gentlegiantJGC/A-Series-of-Unfortunate-Events-Spyglass/Photos/full_1.jpg

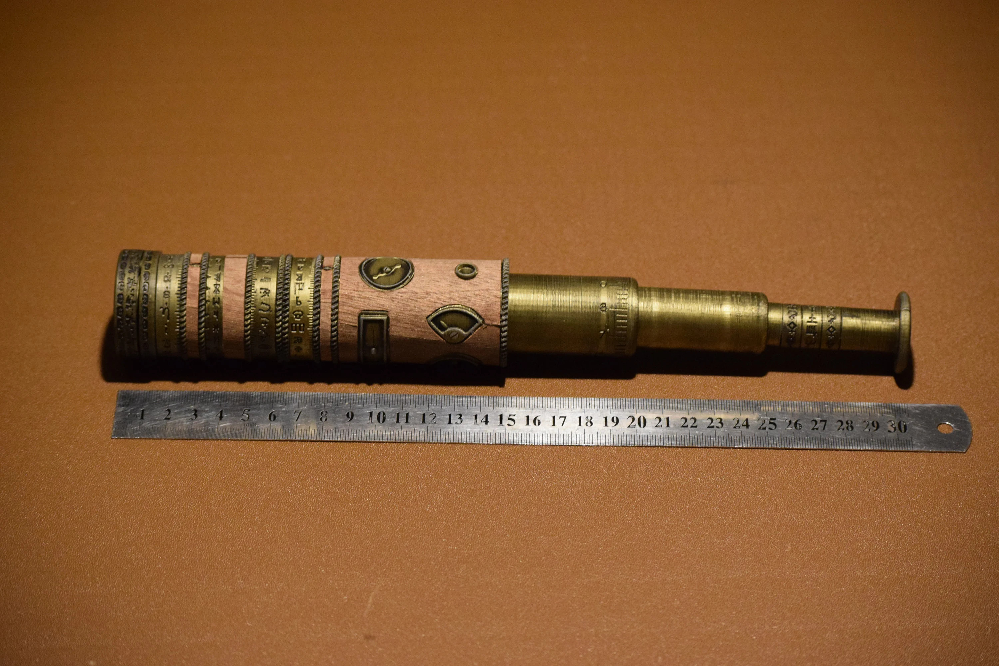
Photos/full_1.jpg
