gentlegiantJGC/A-Series-of-Unfortunate-Events-Spyglass/Photos/full_2.jpg

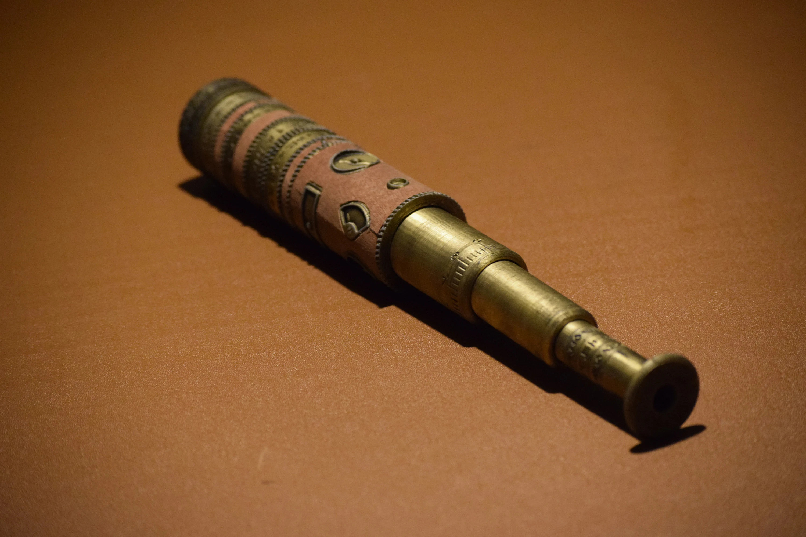
Photos/full_2.jpg
