gentlegiantJGC/A-Series-of-Unfortunate-Events-Spyglass/Photos/head_3.jpg

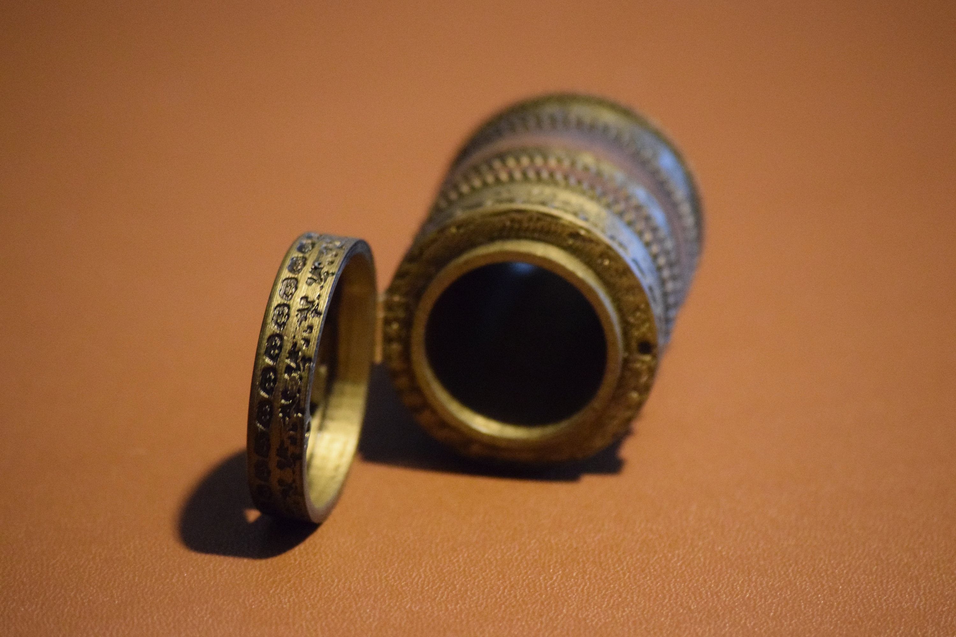
Photos/head_3.jpg
