gentlegiantJGC/A-Series-of-Unfortunate-Events-Spyglass/Photos/head_4.jpg

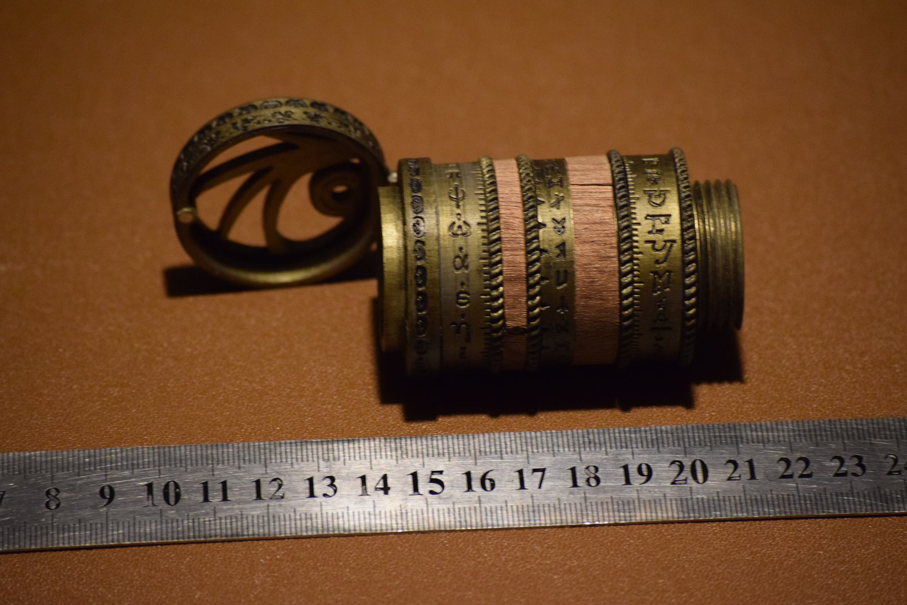
Photos/head_4.jpg
