gentlegiantJGC/A-Series-of-Unfortunate-Events-Spyglass/Photos/head_5.jpg

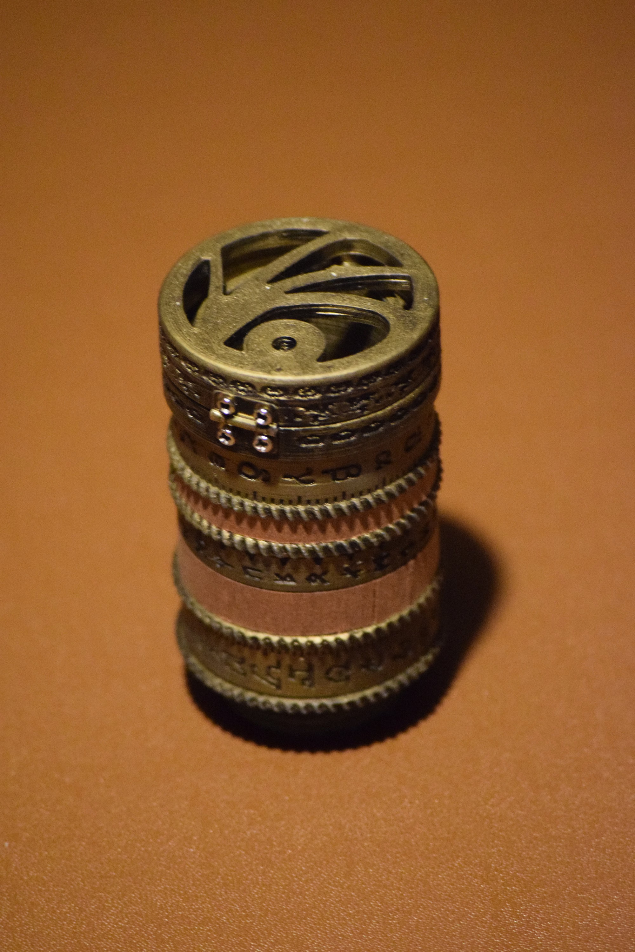
Photos/head_5.jpg
