gentlegiantJGC/A-Series-of-Unfortunate-Events-Spyglass/Photos/head_6.jpg

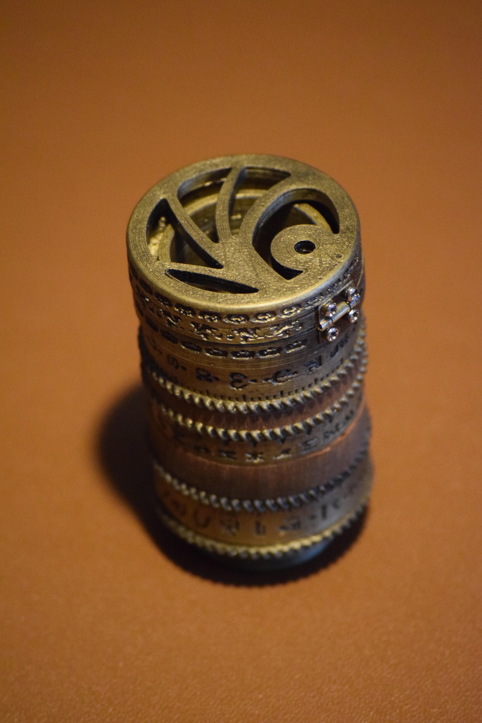
Photos/head_6.jpg
