gentlegiantJGC/A-Series-of-Unfortunate-Events-Spyglass/Photos/head_8.jpg

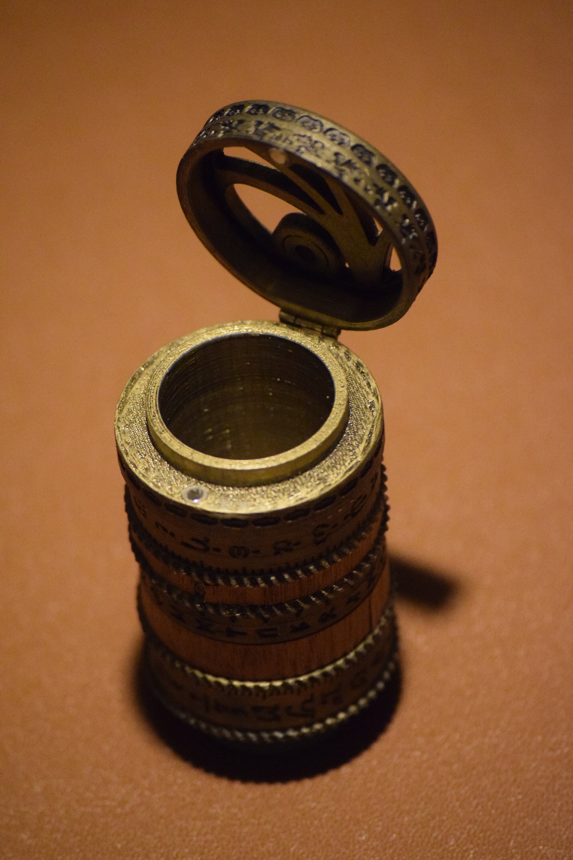
Photos/head_8.jpg
