gentlegiantJGC/A-Series-of-Unfortunate-Events-Spyglass/Photos/head_9.jpg

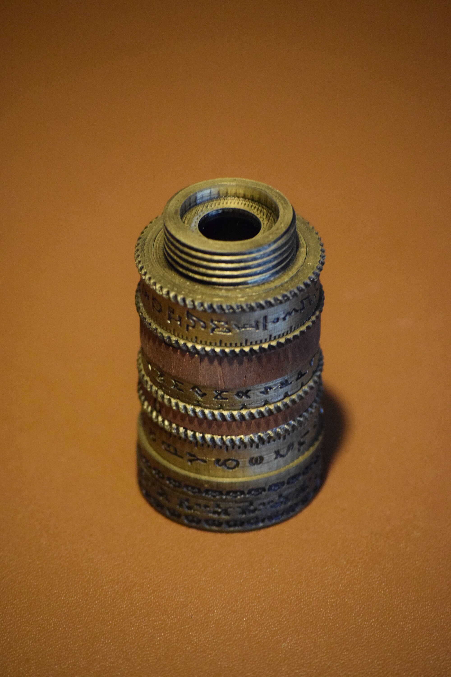
Photos/head_9.jpg
