gentlegiantJGC/A-Series-of-Unfortunate-Events-Spyglass/Photos/head_10.jpg

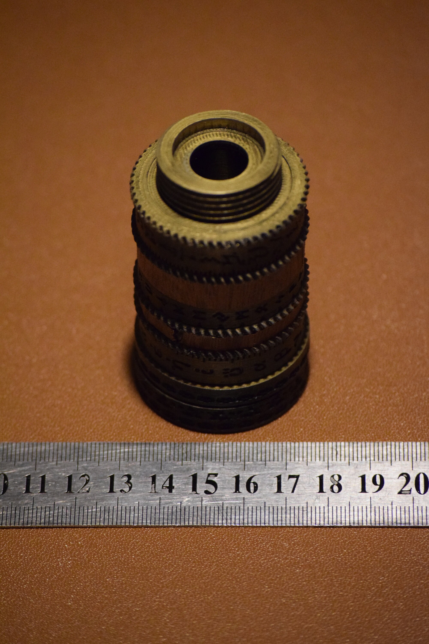
Photos/head_10.jpg
