gentlegiantJGC/A-Series-of-Unfortunate-Events-Spyglass/Photos/head_12.jpg

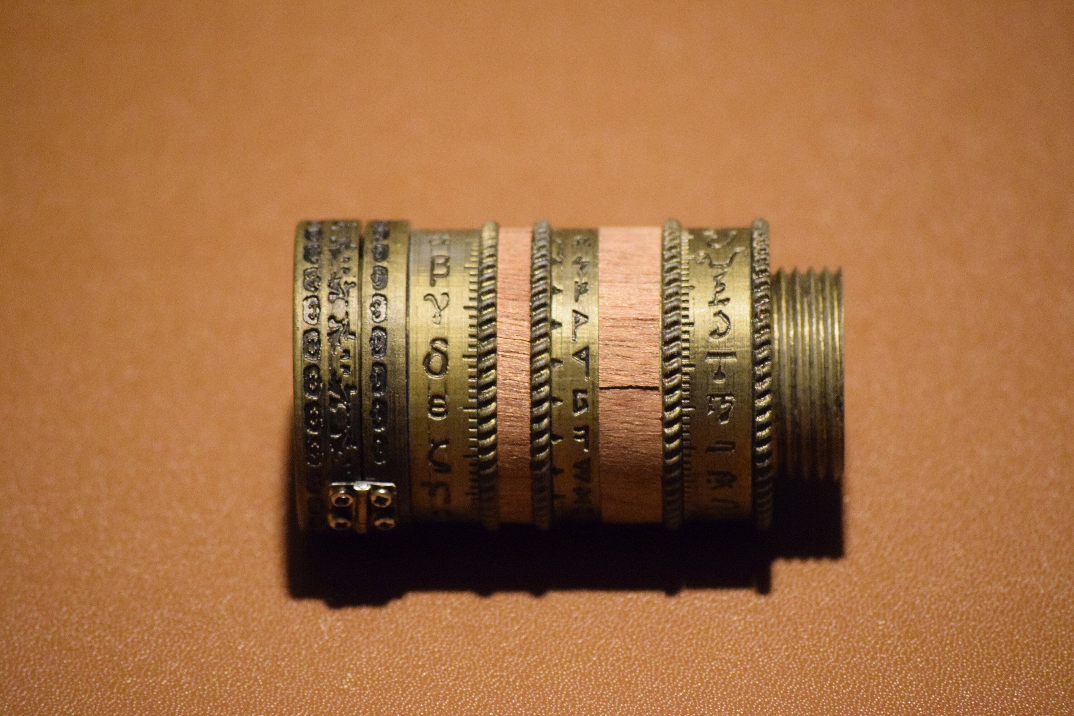
Photos/head_12.jpg
