gentlegiantJGC/A-Series-of-Unfortunate-Events-Spyglass/Photos/head_14.jpg

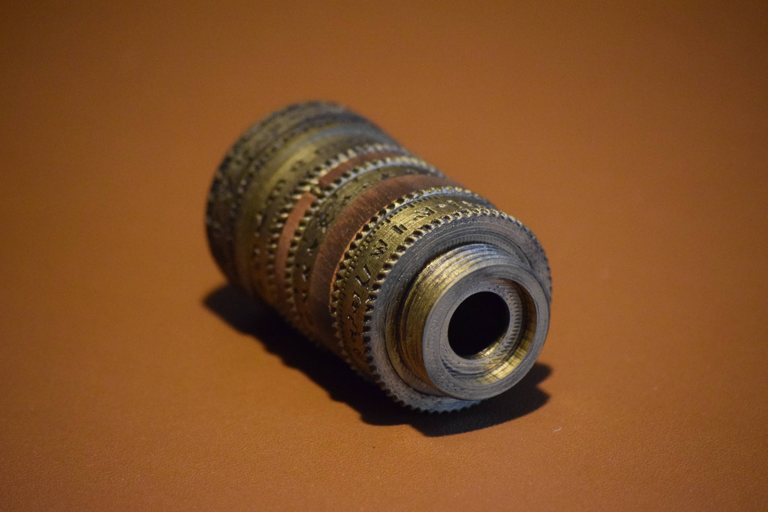
Photos/head_14.jpg
