gentlegiantJGC/A-Series-of-Unfortunate-Events-Spyglass/Photos/head_15.jpg

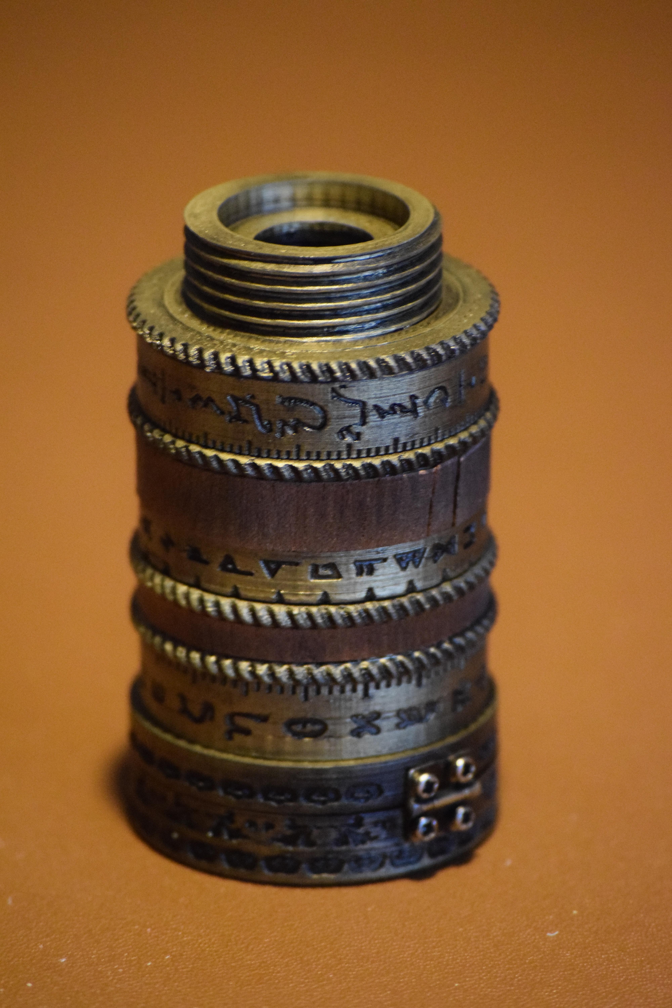
Photos/head_15.jpg
