gentlegiantJGC/A-Series-of-Unfortunate-Events-Spyglass/Photos/head_16.jpg

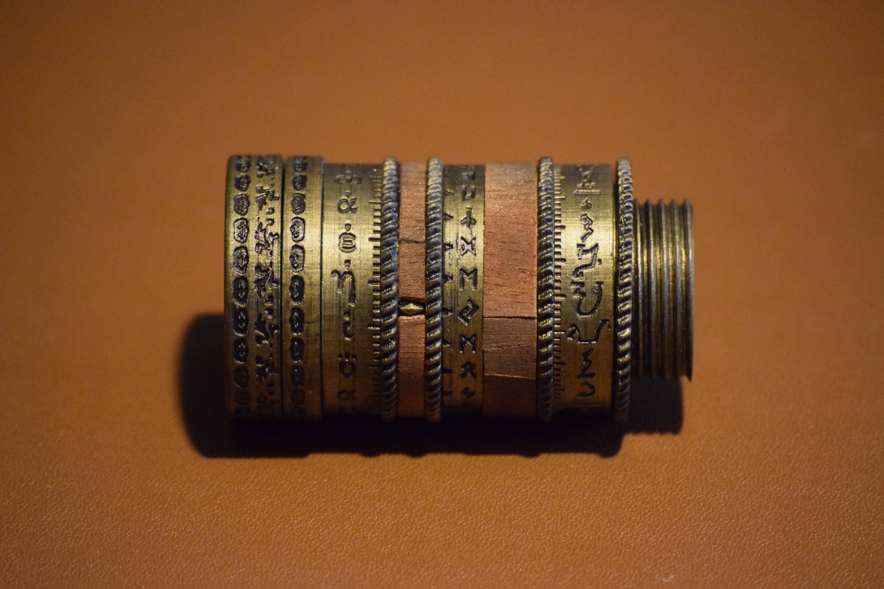
Photos/head_16.jpg
