gentlegiantJGC/A-Series-of-Unfortunate-Events-Spyglass/Photos/head_17.jpg

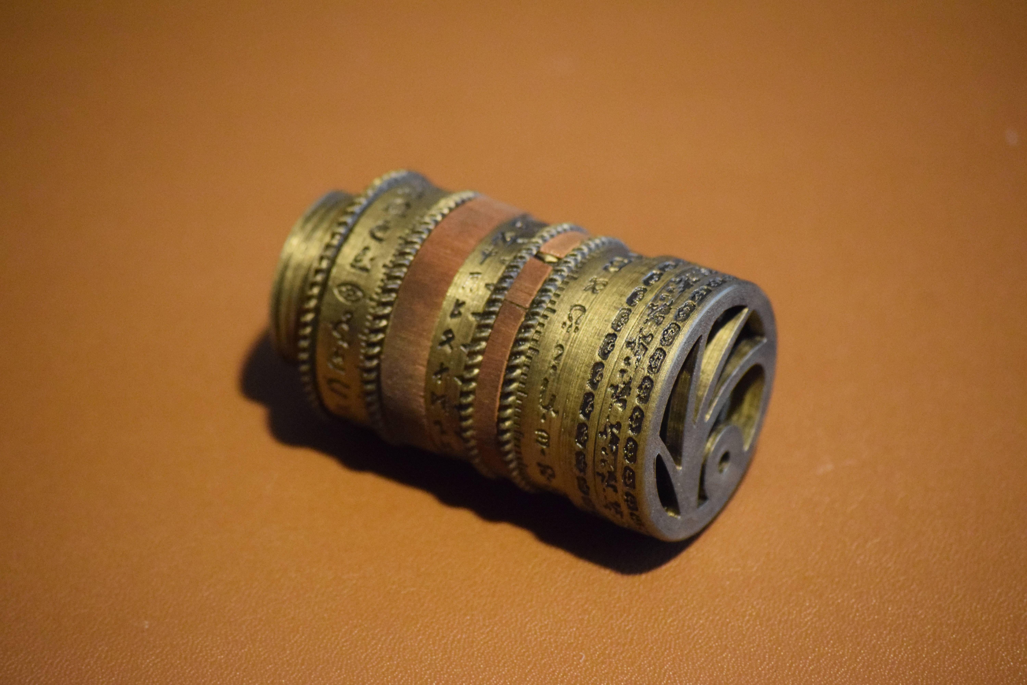
Photos/head_17.jpg
