gentlegiantJGC/A-Series-of-Unfortunate-Events-Spyglass/Photos/tail_1.jpg

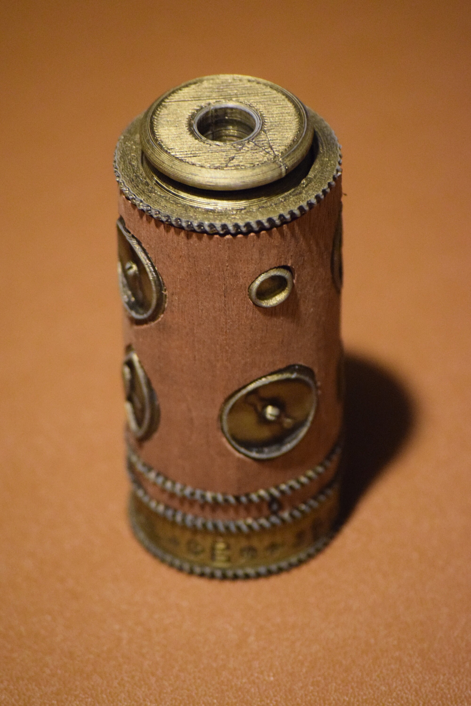
Photos/tail_1.jpg
