gentlegiantJGC/A-Series-of-Unfortunate-Events-Spyglass/Photos/tail_2.jpg

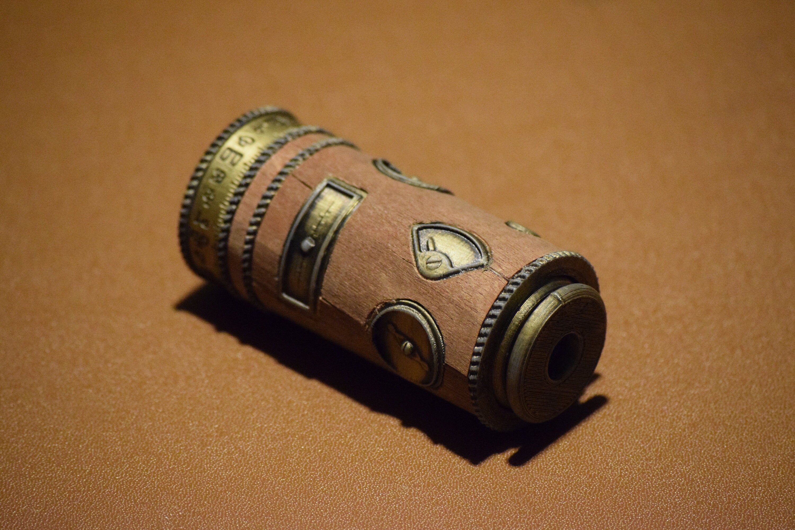
Photos/tail_2.jpg
