gentlegiantJGC/A-Series-of-Unfortunate-Events-Spyglass/Photos/tail_3.jpg

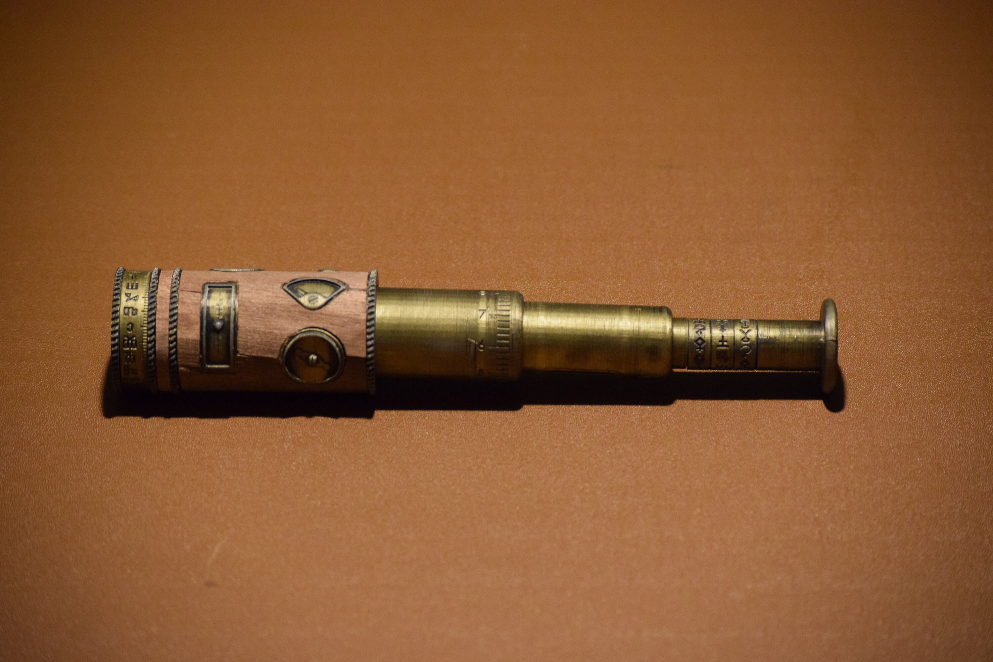
Photos/tail_3.jpg
