gentlegiantJGC/A-Series-of-Unfortunate-Events-Spyglass/Photos/tail_5.jpg

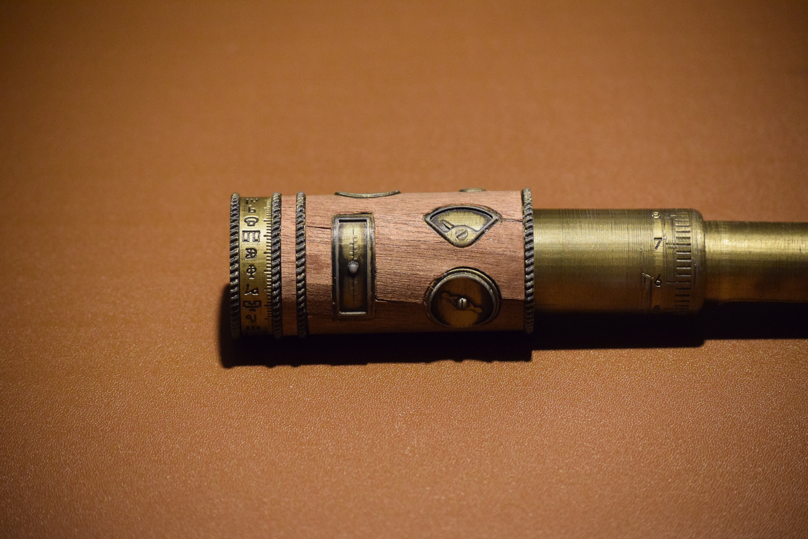
Photos/tail_5.jpg
