gentlegiantJGC/A-Series-of-Unfortunate-Events-Spyglass/Photos/tail_7.jpg

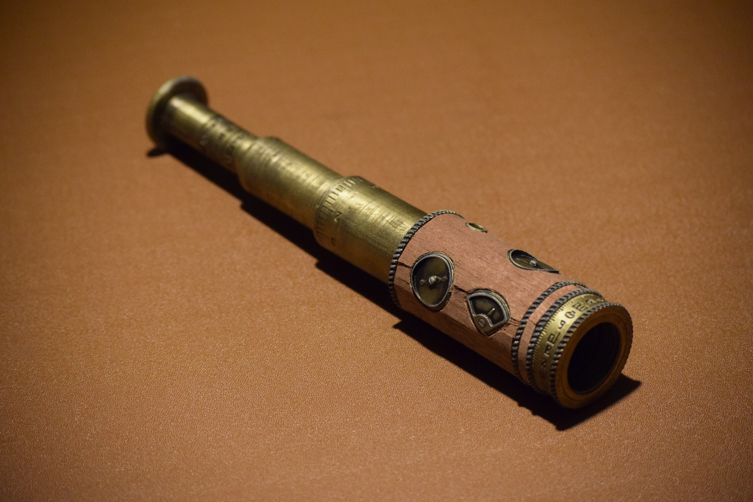
Photos/tail_7.jpg
