gentlegiantJGC/A-Series-of-Unfortunate-Events-Spyglass/Photos/tail_8.jpg

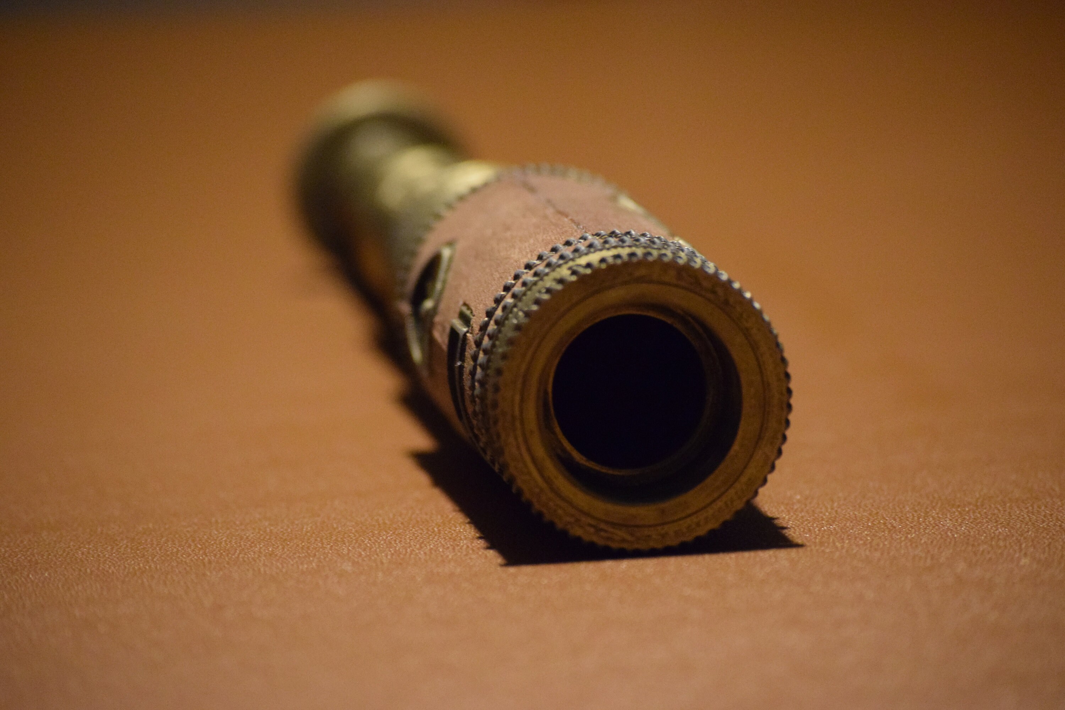
Photos/tail_8.jpg
