gentlegiantJGC/A-Series-of-Unfortunate-Events-Spyglass/Photos/tail_9.jpg

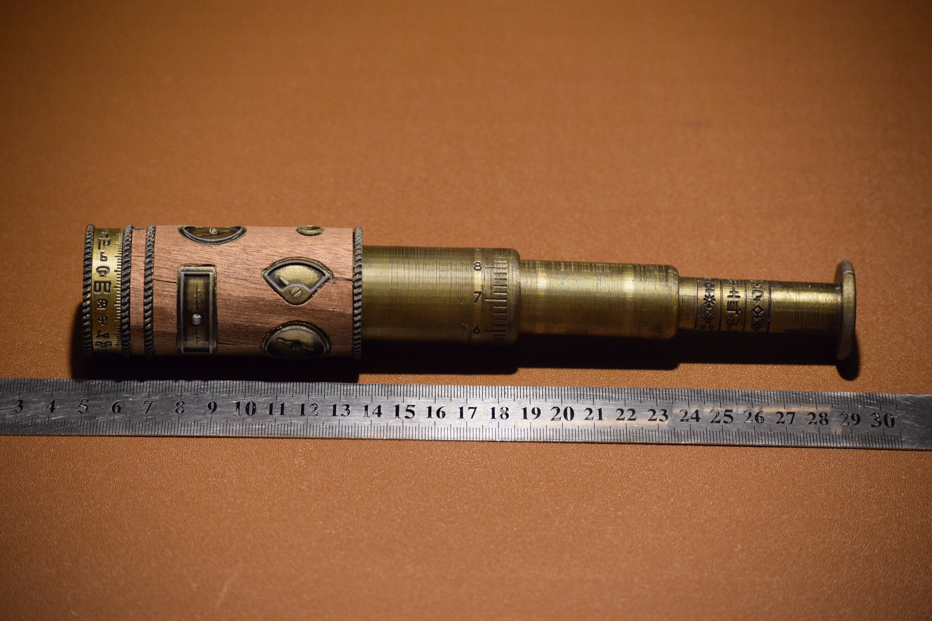
Photos/tail_9.jpg
