gentlegiantJGC/A-Series-of-Unfortunate-Events-Spyglass/Photos/tail_10.jpg

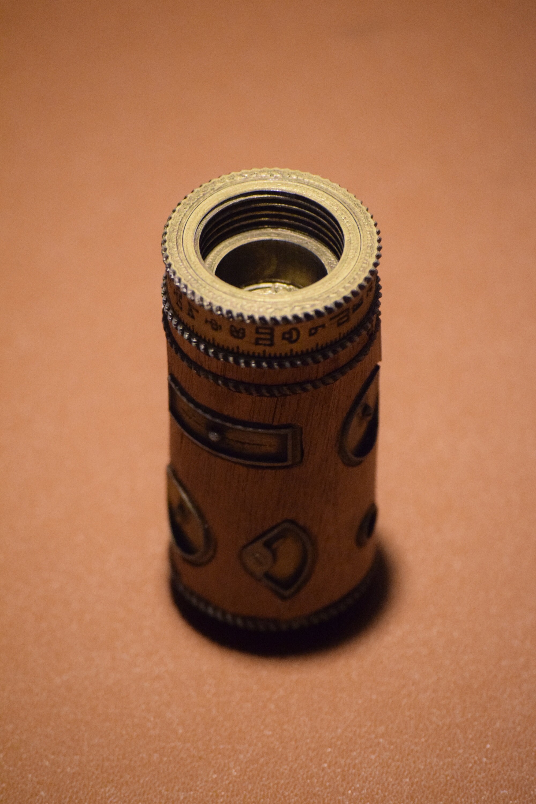
Photos/tail_10.jpg
