gentlegiantJGC/A-Series-of-Unfortunate-Events-Spyglass/STL/head/ring3/magiRingIncrements.STL

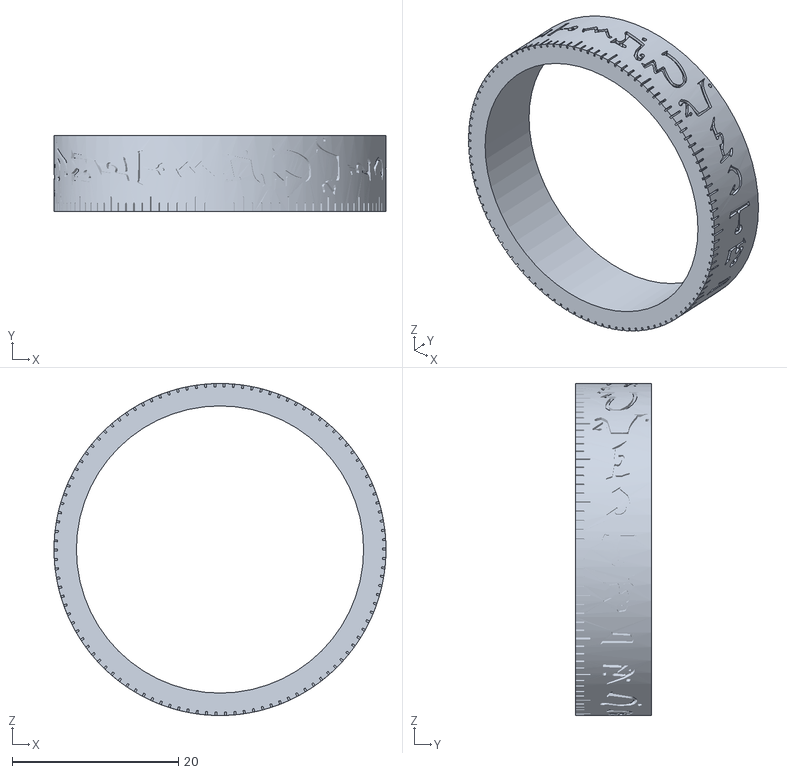
[picture p45: CAD file, 2024-02-23]
STL/head/ring3/magiRingIncrements.STL
40.0 x 9.15 x 40.0
