gentlegiantJGC/A-Series-of-Unfortunate-Events-Spyglass/STL/telescope/telescopeMedium.STL

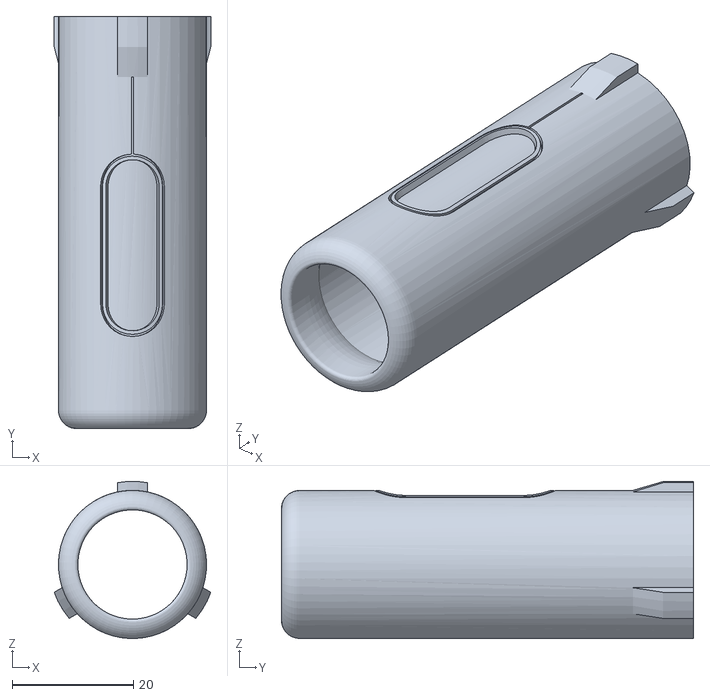
[picture p46: CAD file, 2024-02-23]
STL/telescope/telescopeMedium.STL
25.8 x 67.9 x 25.9
