gentlegiantJGC/A-Series-of-Unfortunate-Events-Spyglass/Solidworks Source/tail/tailDials.SLDPRT

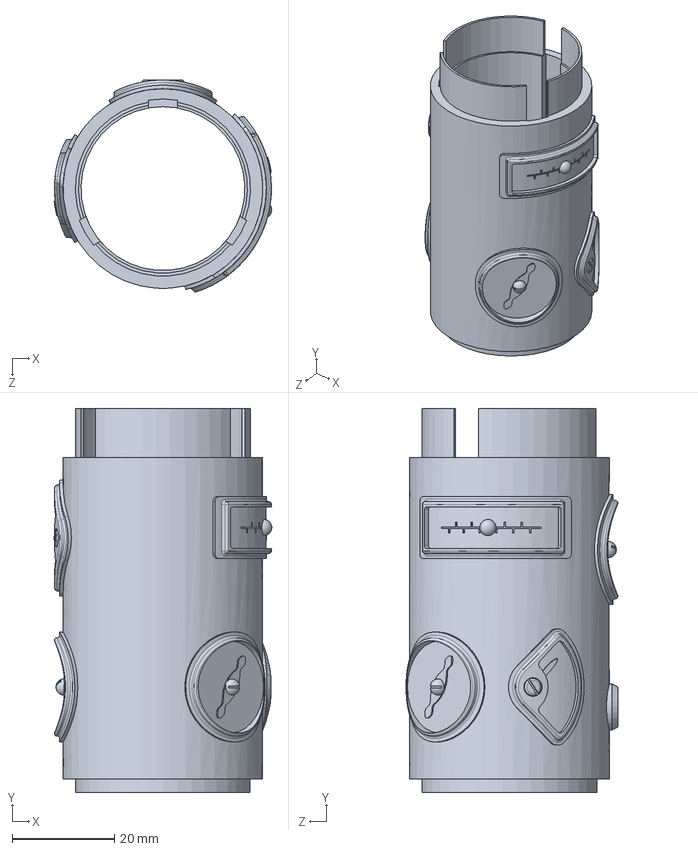
[picture p47: CAD file, 2024-02-23]
Solidworks Source/tail/tailDials.SLDPRT
42.5 x 75.0 x 41.4 mm
