gentlegiantJGC/A-Series-of-Unfortunate-Events-Spyglass/Solidworks Source/teliscope/telescope_ring2.SLDPRT

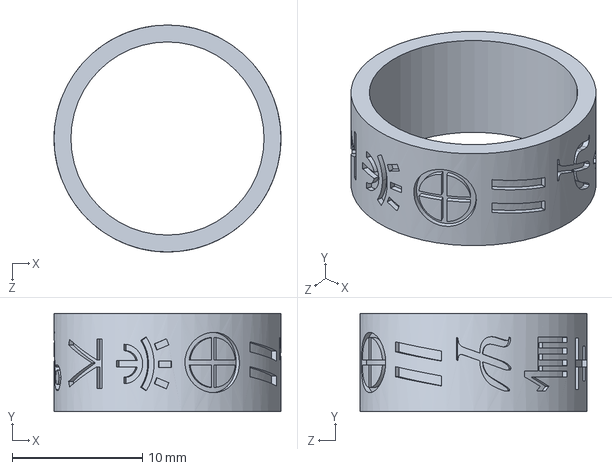
[picture p48: CAD file, 2024-02-23]
Solidworks Source/teliscope/telescope_ring2.SLDPRT
17.4 x 7.53 x 17.4 mm
