gentlegiantJGC/A-Series-of-Unfortunate-Events-Spyglass/STL/telescope/telescopeSmall_part2.STL

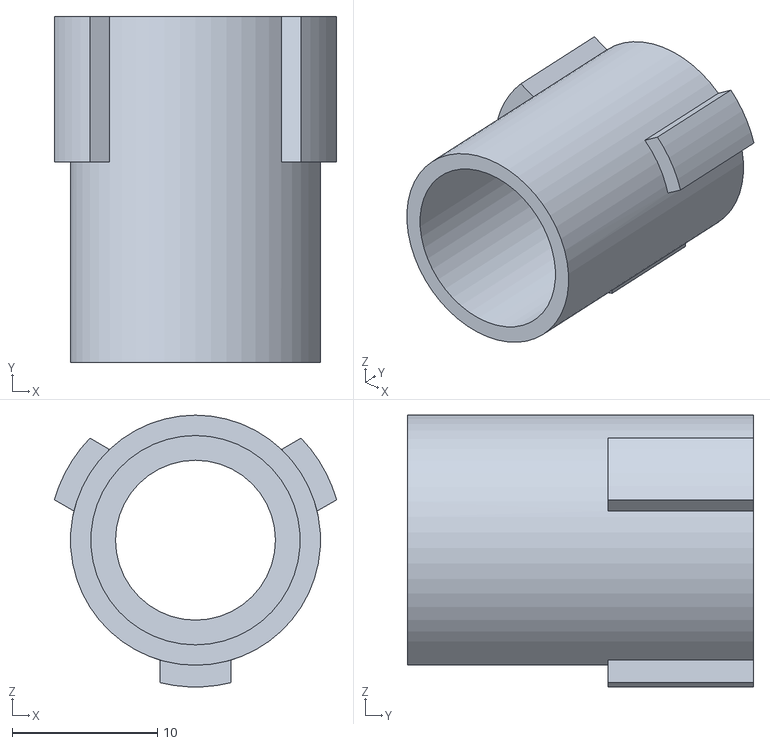
[picture p49: CAD file, 2024-02-23]
STL/telescope/telescopeSmall_part2.STL
19.4 x 23.8 x 18.7
