gentlegiantJGC/A-Series-of-Unfortunate-Events-Spyglass/Solidworks Source/tail/ruby.SLDPRT

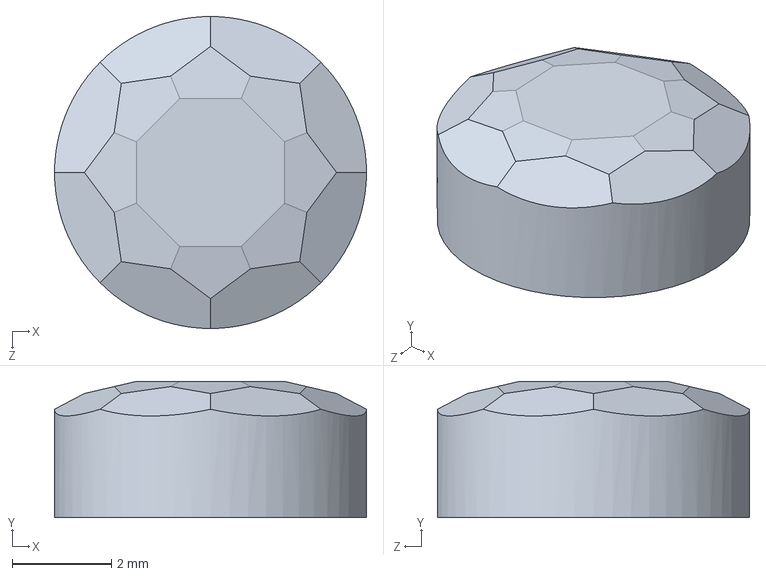
[picture p50: CAD file, 2024-02-23]
Solidworks Source/tail/ruby.SLDPRT
6.30 x 2.75 x 6.30 mm
