gentlegiantJGC/A-Series-of-Unfortunate-Events-Spyglass/Solidworks Source/head/vfd_veneer_template.SLDPRT

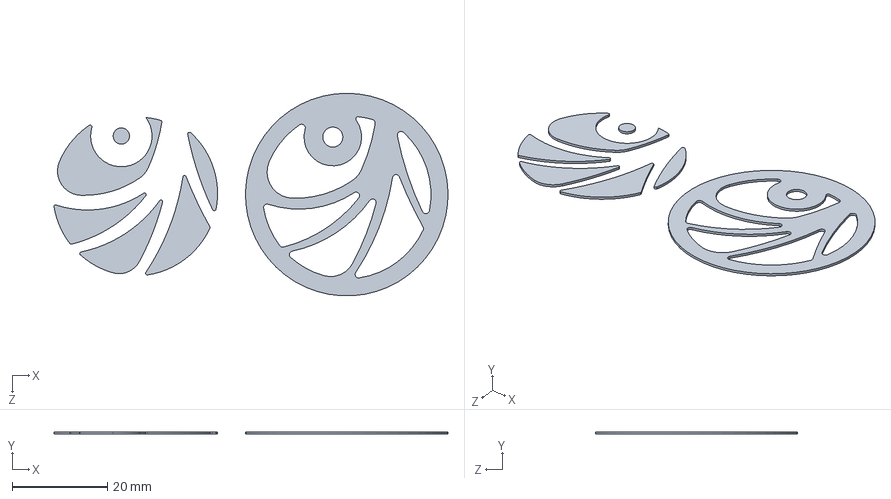
[picture p51: CAD file, 2024-02-23]
Solidworks Source/head/vfd_veneer_template.SLDPRT
82.9 x 0.5 x 42.6 mm
