gentlegiantJGC/A-Series-of-Unfortunate-Events-Spyglass/Solidworks Source/teliscope/telescopeLarge.SLDPRT

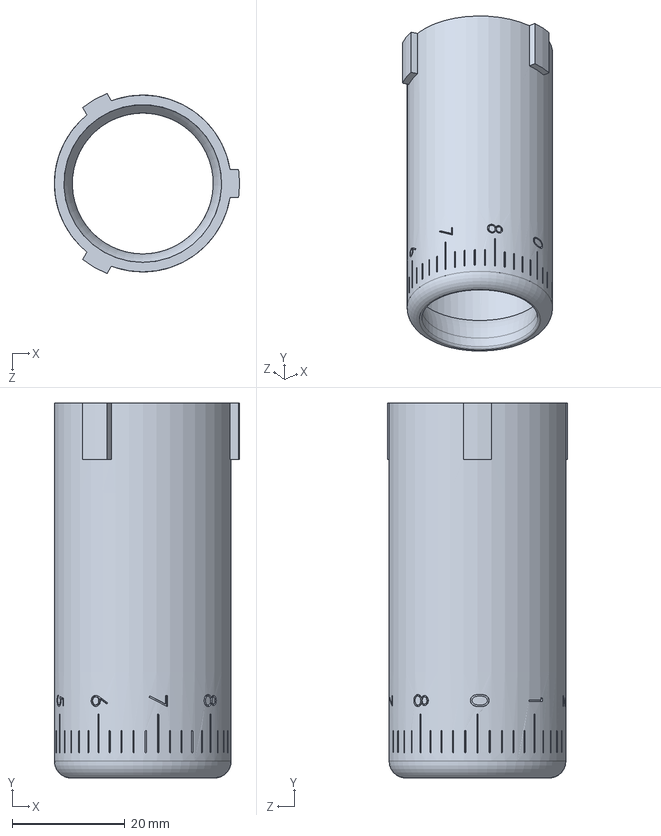
[picture p53: CAD file, 2024-02-23]
Solidworks Source/teliscope/telescopeLarge.SLDPRT
32.9 x 66.6 x 32.0 mm
